ranveerlabs/morphcpu/gateware/rtl/morphcpu_top.v

`timescale 1ns / 1ps
`default_nettype none

module morphcpu_top #(
    parameter CLK_HZ = 16_000_000,
    parameter BAUD   = 115_200,
    parameter DATA_W = 8,
    parameter ROWS   = 4,
    parameter COLS   = 4,
    parameter LED_ACTIVE_LOW = 0
) (
    input  wire        clk,
    input  wire        rst_n,
    input  wire        uart_rx_i,
    output wire        uart_tx_o,
    output wire [15:0] led
);

    reg [7:0] por_cnt = 8'd0;
    wire      por_done = &por_cnt;

    always @(posedge clk) begin
        if (!por_done)
            por_cnt <= por_cnt + 8'd1;
    end

    reg btn_m, btn_s;
    always @(posedge clk) begin
        btn_m <= rst_n;
        btn_s <= btn_m;
    end

    wire rst = !por_done || !btn_s;

    wire [7:0] rx_data;
    wire       rx_valid;
    wire       rx_frame_err;

    uart_rx #(
        .CLK_HZ   (CLK_HZ),
        .BAUD     (BAUD)
    ) u_rx (
        .clk      (clk),
        .rst      (rst),
        .rx       (uart_rx_i),
        .data     (rx_data),
        .valid    (rx_valid),
        .frame_err(rx_frame_err)
    );

    reg  [7:0] tx_byte;
    reg        tx_send;
    wire       tx_busy;

    uart_tx #(
        .CLK_HZ (CLK_HZ),
        .BAUD   (BAUD)
    ) u_tx (
        .clk    (clk),
        .rst    (rst),
        .data   (tx_byte),
        .send   (tx_send),
        .tx     (uart_tx_o),
        .busy   (tx_busy)
    );

    wire                   cfg_shift;
    wire                   cfg_bit;
    wire                   tick;
    wire                   clr;
    wire [ROWS*DATA_W-1:0] west_in_data;
    wire [ROWS-1:0]        west_in_val;
    wire                   loading;

    config_loader #(
        .DATA_W      (DATA_W),
        .ROWS        (ROWS)
    ) u_cfg (
        .clk         (clk),
        .rst         (rst),
        .rx_data     (rx_data),
        .rx_valid    (rx_valid),
        .cfg_shift   (cfg_shift),
        .cfg_bit     (cfg_bit),
        .tick        (tick),
        .clr         (clr),
        .west_in_data(west_in_data),
        .west_in_val (west_in_val),
        .loading     (loading)
    );

    wire [ROWS*DATA_W-1:0] east_out_data;
    wire [ROWS-1:0]        east_out_val;
    wire [ROWS*COLS-1:0]   cell_active;

    grid #(
        .DATA_W       (DATA_W),
        .ROWS         (ROWS),
        .COLS         (COLS)
    ) u_grid (
        .clk          (clk),
        .rst          (rst),
        .clr          (clr),
        .cfg_shift    (cfg_shift),
        .cfg_in       (cfg_bit),
        .cfg_out      (),
        .tick         (tick),
        .west_in_data (west_in_data),
        .west_in_val  (west_in_val),
        .east_out_data(east_out_data),
        .east_out_val (east_out_val),
        .active       (cell_active)
    );

    reg [ROWS-1:0]        orders;
    reg [ROWS*DATA_W-1:0] plate;

    reg tick_d;
    always @(posedge clk) begin
        if (rst || clr) tick_d <= 1'b0;
        else            tick_d <= tick;
    end

    wire [1:0] nxt_row = orders[0] ? 2'd0 :
                         orders[1] ? 2'd1 :
                         orders[2] ? 2'd2 : 2'd3;

    always @(posedge clk) begin
        if (rst || clr) begin
            orders    <= {ROWS{1'b0}};
            plate     <= {ROWS*DATA_W{1'b0}};
            tx_send   <= 1'b0;
            tx_byte   <= 8'd0;
        end else begin
            tx_send <= 1'b0;
            if (tick_d) begin
                orders    <= east_out_val;
                plate     <= east_out_data;
            end else if (|orders && !tx_busy && !tx_send) begin
                tx_byte     <= plate[nxt_row*DATA_W +: DATA_W];
                tx_send     <= 1'b1;
                orders[nxt_row] <= 1'b0;
            end
        end
    end

    localparam integer STRETCH_DIV = CLK_HZ / 200;

    reg [16:0] str_cnt = 17'd0;
    wire       str_tick = (str_cnt == STRETCH_DIV[16:0] - 1);

    always @(posedge clk) begin
        if (str_tick)
            str_cnt <= 17'd0;
        else
            str_cnt <= str_cnt + 17'd1;
    end

    genvar gi;
    generate
        for (gi = 0; gi < ROWS*COLS; gi = gi + 1) begin : glow
            reg [3:0] hold = 4'd0;
            always @(posedge clk) begin
                if (rst || clr)
                    hold <= 4'd0;
                else if (cell_active[gi])
                    hold <= 4'hF;
                else if (str_tick && hold != 4'd0)
                    hold <= hold - 4'd1;
            end
            assign led[gi] = LED_ACTIVE_LOW ? ~(hold != 4'd0) : (hold != 4'd0);
        end
    endgenerate

endmodule

`default_nettype wire
